bratwoscht/led-matrix-clock/src/NTPClient_ch.h

#pragma once

#include "Arduino.h"

#include <Udp.h>

#define SEVENZYYEARS 2208988800UL
#define NTP_PACKET_SIZE 48
#define NTP_DEFAULT_LOCAL_PORT 1337
#ifndef __isleap
/* Nonzero if YEAR is a leap year (every 4 years,
   except every 100th isn't, and every 400th is).  */
#define  __isleap(year)  \
  ((year) % 4 == 0 && ((year) % 100 != 0 || (year) % 400 == 0))
#endif

#define SECS_PER_HOUR (long)(60 * 60)
#define SECS_PER_DAY  (long)(SECS_PER_HOUR * 24)

struct tm {
    int tm_sec;     /* seconds after the minute - [0,59] */
    int tm_min;     /* minutes after the hour - [0,59] */
    int tm_hour;    /* hours since midnight - [0,23] */
    int tm_mday;    /* day of the month - [1,31] */
    int tm_mon;     /* months since January - [1,12] */
    int tm_year;    /* year*/
    int tm_wday;    /* days since Sunday - [0,6] */
    int tm_yday;    /* days since January 1 - [0,365] */
    int tm_isdst;   /* daylight savings time flag */
};

class NTPClient {
  private:
    UDP*          _udp;
    bool          _udpSetup       = false;

    const char*   _poolServerName = "time.nist.gov"; // Default time server
    int           _port           = NTP_DEFAULT_LOCAL_PORT;
    int           _timeOffset     = 0;

    unsigned int  _updateInterval = 60000;  // In ms

    unsigned long _currentEpoc    = 0;      // In s
    unsigned long _lastUpdate     = 0;      // In ms

    byte          _packetBuffer[NTP_PACKET_SIZE];
    int           _day = 0;    // 1..31
    int           _month = 0;  // 1..12
    int           _year = 0;   // 1970..
    int           _weekday;    // days since Sunday - [0,6]
    void          sendNTPPacket();

  public:
    NTPClient(UDP& udp);
    NTPClient(UDP& udp, int timeOffset);
    NTPClient(UDP& udp, const char* poolServerName);
    NTPClient(UDP& udp, const char* poolServerName, int timeOffset);
    NTPClient(UDP& udp, const char* poolServerName, int timeOffset, int updateInterval);

    /**
     * Starts the underlying UDP client with the default local port
     */
    void begin();

    /**
     * Starts the underlying UDP client with the specified local port
     */
    void begin(int port);

    /**
     * This should be called in the main loop of your application. By default an update from the NTP Server is only
     * made every 60 seconds. This can be configured in the NTPClient constructor.
     *
     * @return true on success, false on failure
     */
    bool update();

    /**
     * This will force the update from the NTP Server.
     *
     * @return true on success, false on failure
     */
    bool forceUpdate();

    void updateDate();
    int getDay();
    int getMonth();
    int getYear();
    int getHours();
    int getHoursUTC();
    int getMinutes();
    int getSeconds();

    /**
     * Changes the time offset. Useful for changing timezones dynamically
     */
    void setTimeOffset(int timeOffset);

    /**
     * Set the update interval to another frequency. E.g. useful when the
     * timeOffset should not be set in the constructor
     */
    void setUpdateInterval(int updateInterval);

    /**
     * @return time formatted like `hh:mm:ss`
     */
    String getFormattedTime();

    /**
     * @return time in seconds since Jan. 1, 1970
     */
    unsigned long getEpochTime();

    /**
     * Stops the underlying UDP client
     */
    void end();
};
