bratwoscht/led-matrix-clock/src/LM75.cpp

/*
    LM75 - An arduino library for the LM75 temperature sensor
    Copyright (C) 2011  Dan Fekete <thefekete AT gmail DOT com>

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
    You should have received a copy of the GNU General Public License
    along with this program.  If not, see <http://www.gnu.org/licenses/>.
 */

#include <Wire.h>
#include "LM75.h"

LM75::LM75 () {
  address = LM75_ADDRESS;
}

LM75::LM75 (uint8_t addr) {
  address = addr;
}

uint16_t LM75::float2regdata (float temp)
{
  // First multiply by 8 and coerce to integer to get +/- whole numbers
  // Then coerce to word and bitshift 5 to fill out MSB
  return (uint16_t)((int16_t)(temp * 8) << 5);
}

float LM75::regdata2float (uint16_t regdata)
{
  return ((float)(int16_t)regdata / 32) / 8;
}

uint16_t LM75::_register16 (uint8_t reg) {
  Wire.beginTransmission(address);
  Wire.write(reg);	
  Wire.endTransmission();
  
  Wire.requestFrom(address, (uint8_t)2);
  uint16_t regdata = (Wire.read() << 8) | Wire.read();
  return regdata;
}

void LM75::_register16 (uint8_t reg, uint16_t regdata) {
  uint8_t msb = (uint8_t)(regdata >> 8);
  uint8_t lsb = (uint8_t)(regdata);
  
  Wire.beginTransmission(address);
  Wire.write(reg);
  Wire.write(msb);
  Wire.write(lsb);
  Wire.endTransmission();
}

uint8_t LM75::_register8 (uint8_t reg) {
  Wire.beginTransmission(address);
  Wire.write(reg);	
  Wire.endTransmission();
  
  Wire.requestFrom(address, (uint8_t)1);
  return Wire.read();
}

void LM75::_register8 (uint8_t reg, uint8_t regdata) {  
  Wire.beginTransmission(address);
  Wire.write(reg);
  Wire.write(regdata);
  Wire.endTransmission();
}

float LM75::temp (void) {
  return regdata2float(_register16(LM75_TEMP_REGISTER));
}

uint8_t LM75::conf () {
  return _register8(LM75_CONF_REGISTER);
}

void LM75::conf (uint8_t data) {
  _register8(LM75_CONF_REGISTER, data);
}

float LM75::tos () {
  return regdata2float(_register16(LM75_TOS_REGISTER));
}

void LM75::tos (float temp) {
  _register16(LM75_TOS_REGISTER, float2regdata(temp));
}

float LM75::thyst () {
  return regdata2float(_register16(LM75_THYST_REGISTER));
}

void LM75::thyst (float temp) {
  _register16(LM75_THYST_REGISTER, float2regdata(temp));
}

boolean LM75::shutdown () {
  return conf() & 0x01;
}

void LM75::shutdown (boolean val) {
  conf(val << LM75_CONF_SHUTDOWN);
}
